afiskon/hbr-cw/firmware/Src/spur_masking.c

#include "spur_masking.h"

// Spurs seem to be inevitable in a 2-IF homebrew receiver. At least I didn't
// manage to get rid of them using filters or shields. They can be masked
// though, by changing CLAR and/or SHIFT just a bit. It is worth noticing that
// I live in a noisy area and my power supply is not particularly clean, so not
// all listed frequencies are necessarily real spurs. Also most of them are
// barely hearable, but I decided to hide them anyway because I could.

// Also, consider tweaking IF2Frequency variable.

// Keep the list sorted by frequency, otherwise getSpurMaskingInfo()
// procedure will not work!
static const SpurMaskInfo SpurMaskInfoArray[] = {
	// 80 meters
	{ 3500200, 0, 10, false },
	{ 3501300, 0, 10, false },
	{ 3501600, 50, 0, false },
	{ 3501700, 50, 0, false },
	{ 3502000, 0, -10, false },
	{ 3503400, 50, 0, false },
	{ 3503700, 0, 10, false },
	{ 3503800, 0, 10, false },
	{ 3504100, 0, 10, false },
	{ 3505500, 0, -10, false },
	{ 3505600, 0, -40, false },
	{ 3505800, 0, -20, false },
	{ 3505900, 50, -20, false },
	{ 3506000, 0, -30, false },
	{ 3506100, 0, -50, false },
	{ 3506200, 0, -40, false },
	{ 3506300, 0, -100, false },
	{ 3506400, 0, 50, false },
	{ 3506500, 0, 50, false },
	{ 3506600, 0, 20, false },
	{ 3506900, -50, 0, false },
	{ 3507900, 0, -10, false },
	{ 3510000, 0, -20, false },
	{ 3512400, 0, -10, false },
	{ 3513500, 50, 0, false },
	{ 3517700, -50, 0, false },
	{ 3520000, 0, 20, false },
	{ 3520200, 0, -10, false },
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
	while(left <= right) {
		int current = (left + right) / 2;
		if(SpurMaskInfoArray[current].freq == freq) {
			return &SpurMaskInfoArray[current];
		}

		if(SpurMaskInfoArray[current].freq > freq) {
			right = current - 1;
		} else {
			left = current + 1;
		}
	}

	/* not found */
	return NULL;
}
