afiskon/hbr-cw/firmware/Src/spur_masking.h

#ifndef _SPURS_MASKING_H_
#define _SPURS_MASKING_H_

#include <stdint.h>
#include <stdbool.h>
#include <stddef.h>

typedef struct {
	int32_t freq;
	int32_t clar;
	int32_t shift;
	bool useAlternativeIF2Frequency;
} SpurMaskInfo;

bool isSpurMaskingInfoSorted(int32_t* first_mismatch);
const SpurMaskInfo* getSpurMaskingInfo(int32_t freq);

#endif // _SPURS_MASKING_H_
